elliotf/cranestyle-mini/renders/x-min-cover.stl

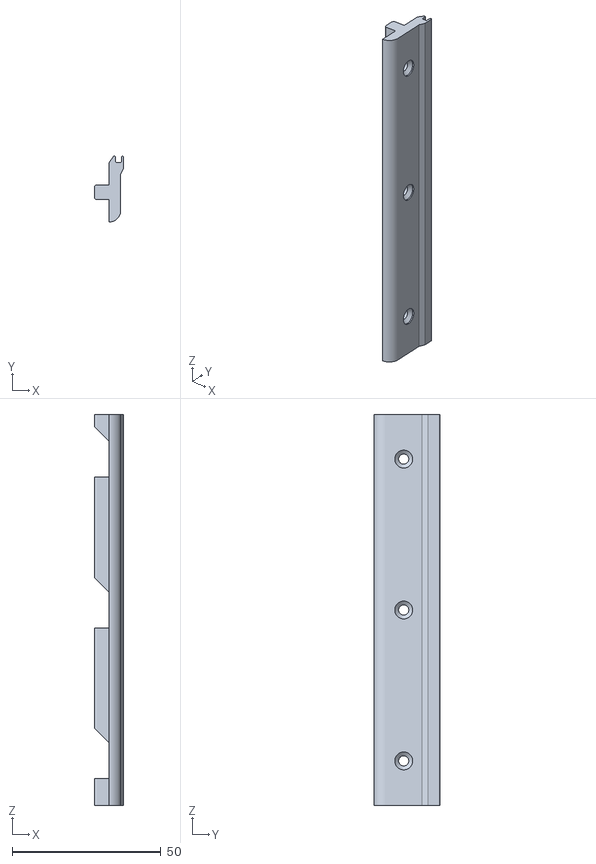
[picture p15: CAD file, 2019-06-30]
renders/x-min-cover.stl
9.90 x 22.2 x 131.5
