elliotf/cranestyle-mini/walter/Left Extruder Cable Clip.stl

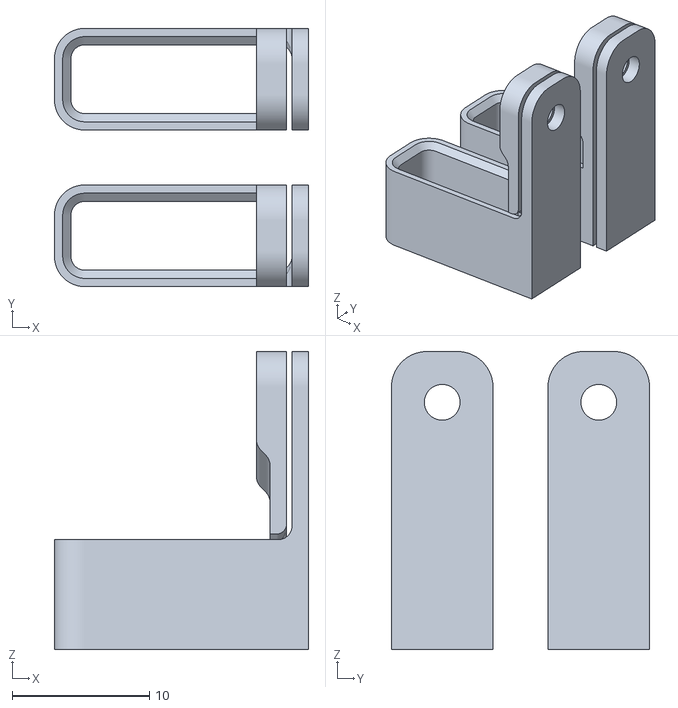
[picture p16: CAD file, 2019-05-31]
walter/Left Extruder Cable Clip.stl
18.5 x 18.8 x 21.7
