elliotf/cranestyle-mini/renders/y-endstop-mount.stl

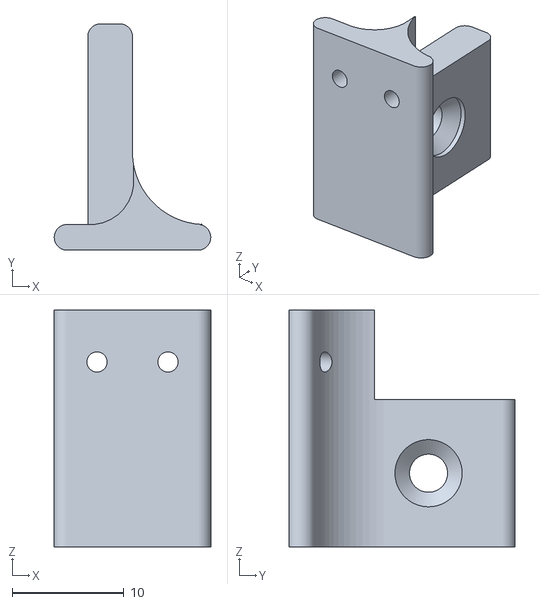
[picture p17: CAD file, 2019-06-30]
renders/y-endstop-mount.stl
14.0 x 20.2 x 21.2
