elliotf/cranestyle-mini/renders/x-max-cover.stl

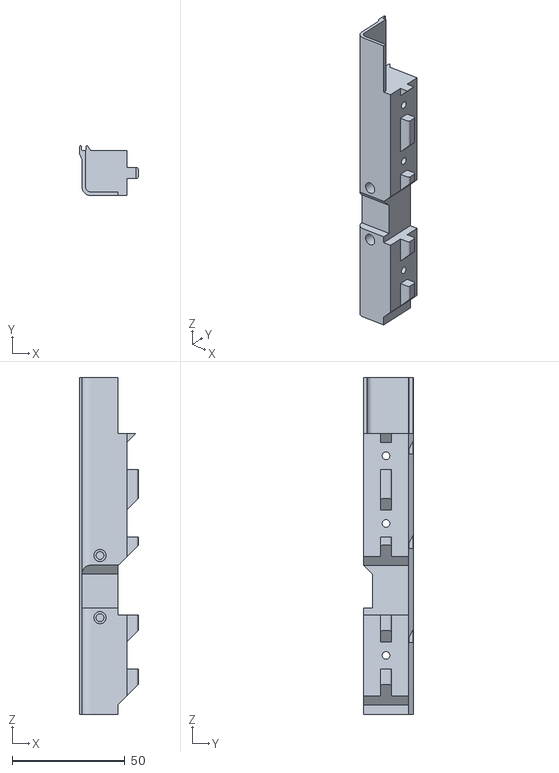
[picture p18: CAD file, 2019-06-30]
renders/x-max-cover.stl
26.0 x 22.2 x 149.5
