elliotf/cranestyle-mini/renders/z-motor-mount.stl

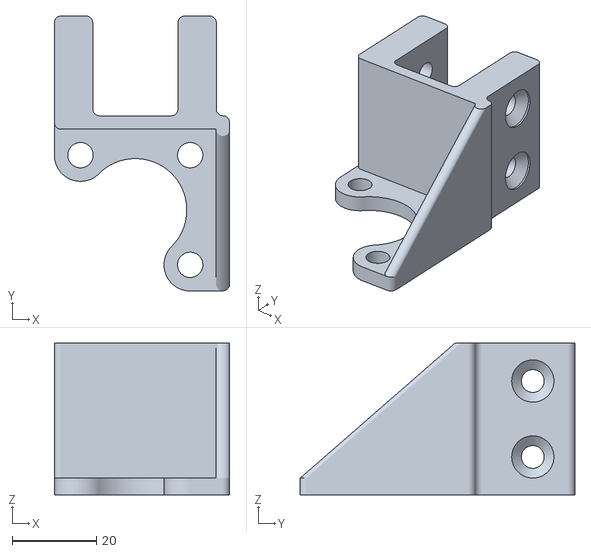
[picture p19: CAD file, 2019-06-30]
renders/z-motor-mount.stl
41.5 x 65.2 x 36.0
