elliotf/cranestyle-mini/renders/tnut-zip-tie-anchor.stl

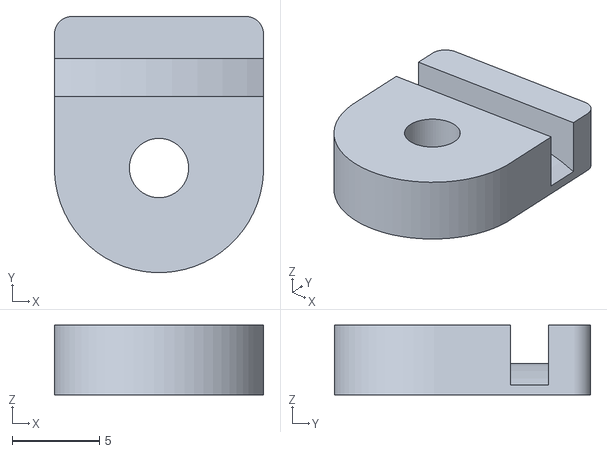
[picture p20: CAD file, 2019-06-30]
renders/tnut-zip-tie-anchor.stl
12.0 x 14.7 x 4.00
