elliotf/cranestyle-mini/renders/y-belt-carriage-mount.stl

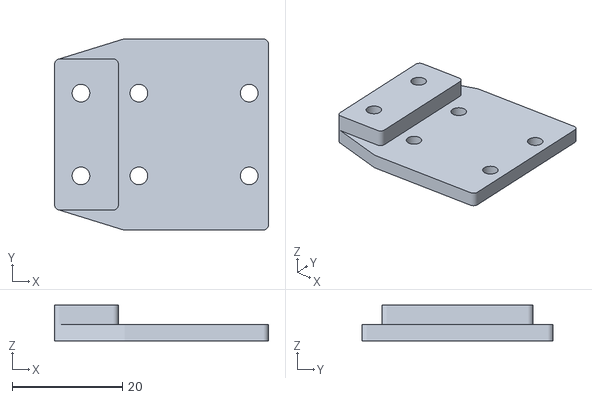
[picture p21: CAD file, 2019-06-30]
renders/y-belt-carriage-mount.stl
38.8 x 34.7 x 6.50
