elliotf/cranestyle-mini/renders/end-cap-rear.stl

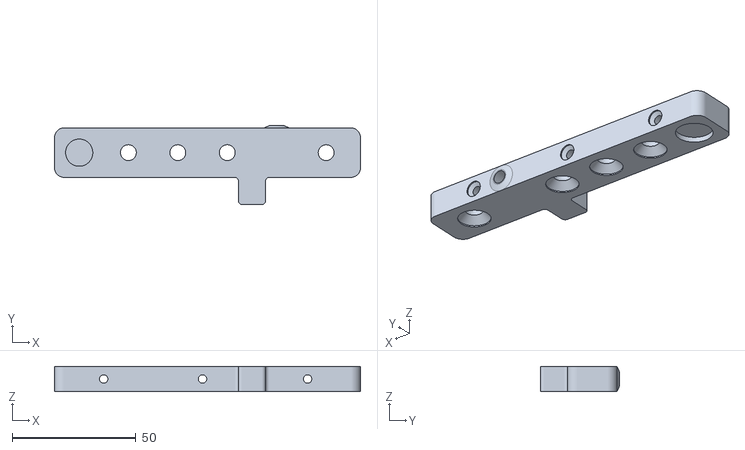
[picture p22: CAD file, 2019-06-30]
renders/end-cap-rear.stl
123.8 x 32.0 x 10.2
