elliotf/cranestyle-mini/renders/tnut-cable-clip.stl

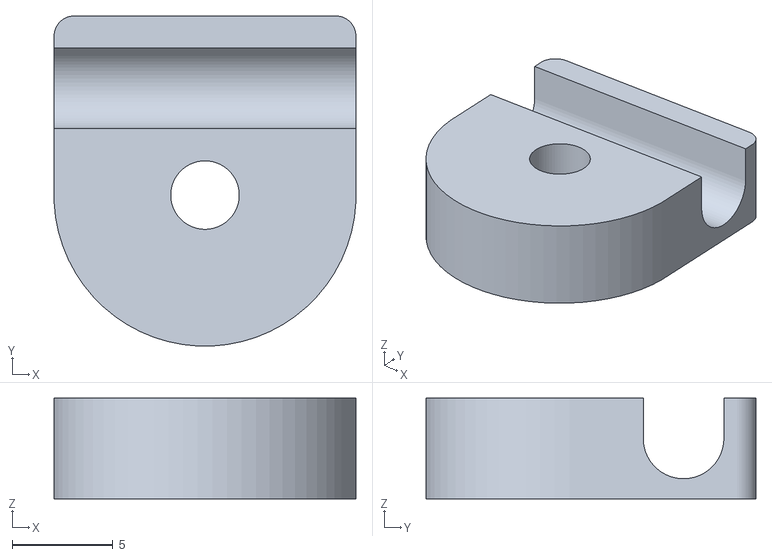
[picture p23: CAD file, 2019-06-30]
renders/tnut-cable-clip.stl
15.0 x 16.4 x 5.00
