elliotf/cranestyle-mini/renders/extruder-motor-plate.stl

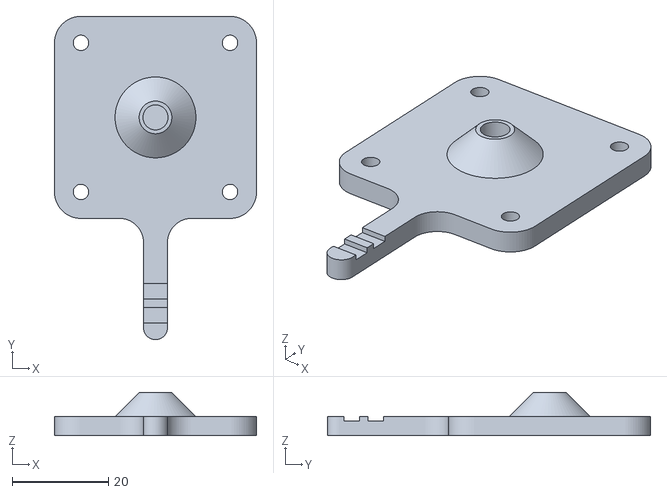
[picture p24: CAD file, 2019-06-30]
renders/extruder-motor-plate.stl
42.0 x 67.2 x 9.00
