elliotf/cranestyle-mini/renders/y-belt-clamp.stl

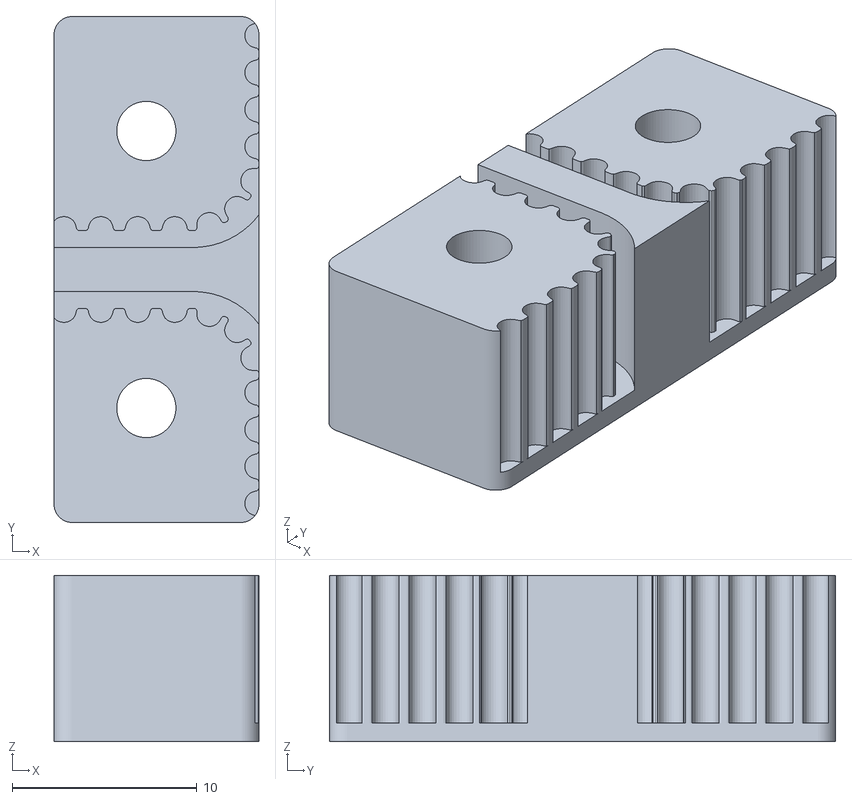
[picture p25: CAD file, 2019-06-30]
renders/y-belt-clamp.stl
11.1 x 27.4 x 9.00
