elliotf/cranestyle-mini/renders/x-idler.stl

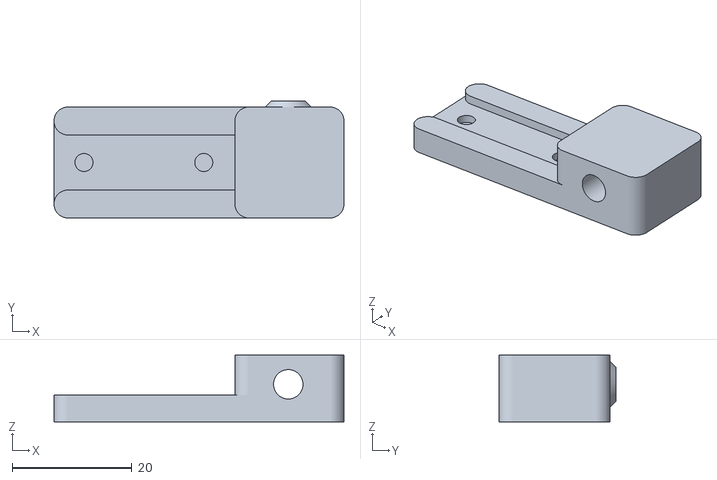
[picture p26: CAD file, 2019-06-30]
renders/x-idler.stl
48.4 x 19.5 x 11.1
