elliotf/cranestyle-mini/renders/tslot-filler.stl

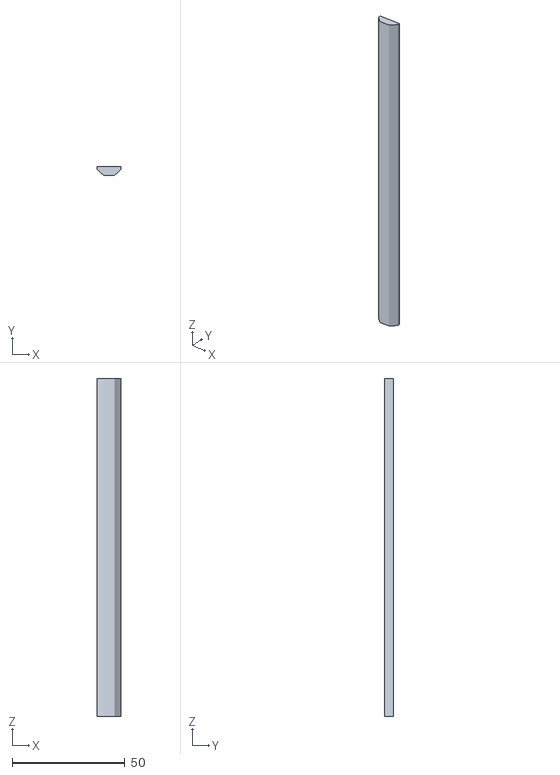
[picture p27: CAD file, 2019-06-15]
renders/tslot-filler.stl
10.6 x 3.80 x 150.0
