elliotf/cranestyle-mini/renders/hotend-fan-mount.stl

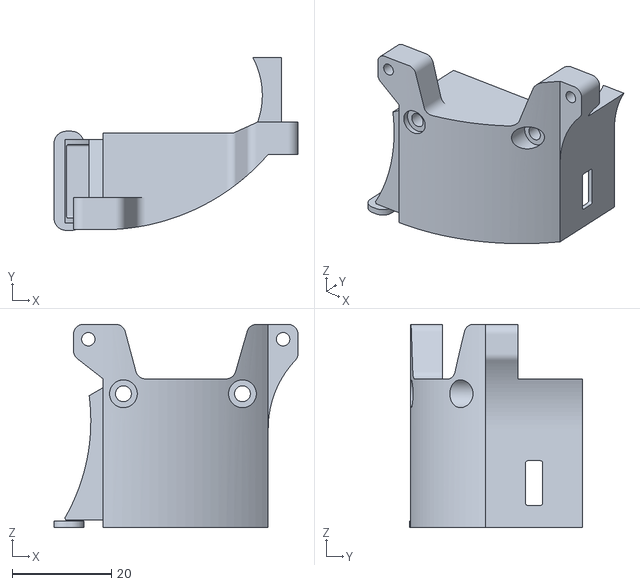
[picture p28: CAD file, 2019-06-15]
renders/hotend-fan-mount.stl
49.2 x 34.9 x 41.0
