elliotf/cranestyle-mini/renders/tnut-cable-anchor.stl

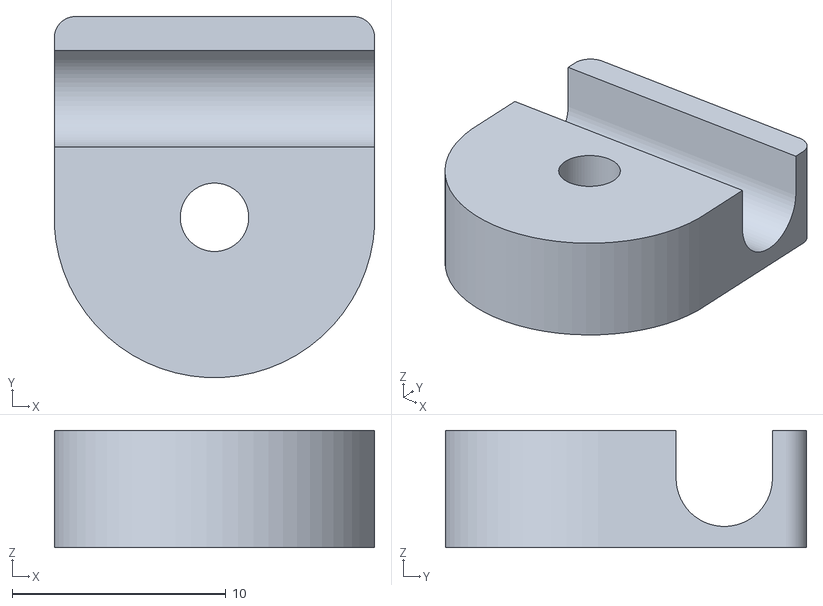
[picture p29: CAD file, 2019-06-06]
renders/tnut-cable-anchor.stl
15.0 x 16.9 x 5.50
