elliotf/cranestyle-mini/renders/m2-tnut.stl

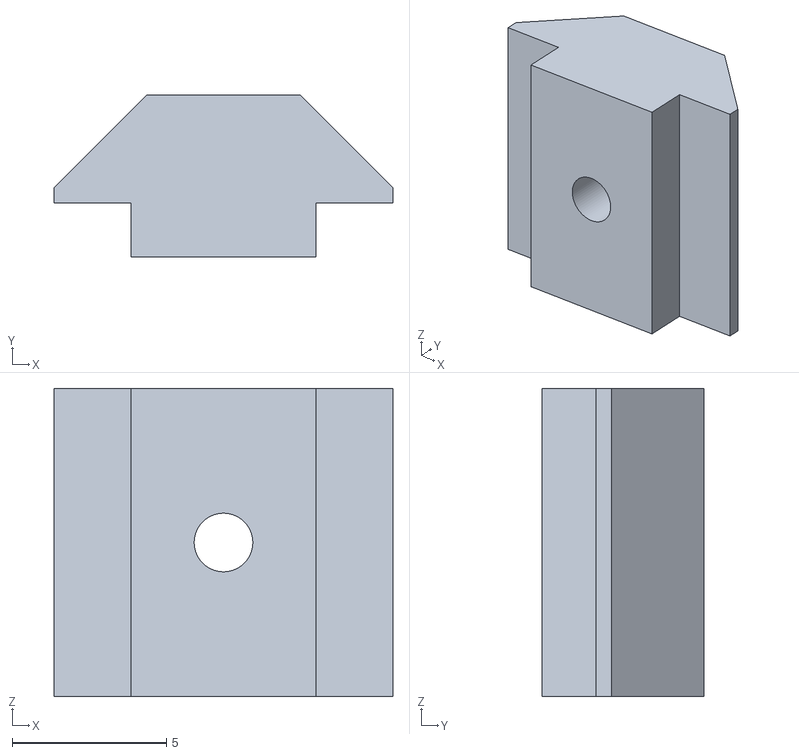
[picture p30: CAD file, 2019-06-04]
renders/m2-tnut.stl
11.0 x 5.25 x 10.0
