elliotf/cranestyle-mini/for_render/extruder-motor-plate.scad

use <../extruder-mount.scad>;

extruder_motor_plate_to_print();
