elliotf/cranestyle-mini/for_render/x-motor-threaded-insert-nut-holder.scad

color("lightblue") import("../walter/20mm Nut Holder.stl");
