elliotf/cranestyle-mini/for_render/y-motor-mount.scad

use <../y-motor-mount.scad>;

to_print();
