elliotf/cranestyle-mini/for_render/z-motor-mount.scad

use <../z-motor-mount.scad>;

to_print();
