elliotf/cranestyle-mini/for_render/bottom_cover.scad

include <../config.scad>;
include <../lib/util.scad>;
use <../end-caps.scad>;

bottom_cover();
