elliotf/cranestyle-mini/for_render/duet-mount.scad

use <../duet-wifi-mount.scad>;

to_print();
