elliotf/cranestyle-mini/for_render/end-cap-rear.scad

include <../config.scad>;
include <../lib/util.scad>;
use <../end-caps.scad>;

rotate([-90,0,0]) {
  end_cap_rear();
}
