elliotf/cranestyle-mini/for_render/extruder-bracket.scad

use <../extruder-mount.scad>;

extruder_bracket_to_print();
