elliotf/cranestyle-mini/for_render/extruder-swivel.scad

use <../extruder-mount.scad>;

extruder_swivel_to_print();
