elliotf/cranestyle-mini/for_render/handle.scad

use <../handle.scad>;

handle();
