elliotf/cranestyle-mini/for_render/hotend-fan-mount.scad

use <../hotend-fan-mount.scad>;

hotend_fan_mount_to_print();
