elliotf/cranestyle-mini/for_render/m2-tnut.scad

use <../tnuts.scad>;

m2_tnut();
