elliotf/cranestyle-mini/for_render/part-cooling-duct.scad

translate([0,0,28.1]) {
  rotate([0,52,0]) {
    color("lightblue") import("../walter/Cooling Duct.stl");
  }
}
