elliotf/cranestyle-mini/for_render/tnut-cable-clip.scad

use <../tslot-stuff.scad>;

tnut_cable_anchor(4);
