elliotf/cranestyle-mini/for_render/tnut-m2-nut.scad

use <../tnuts.scad>;

tnut_m2();
