elliotf/cranestyle-mini/for_render/tnut-zip-tie-anchor.scad

use <../tslot-stuff.scad>;

tnut_zip_tie_anchor();
