elliotf/cranestyle-mini/for_render/tslot-filler.scad

use <../tslot-stuff.scad>;

tslot_filler(150);
