elliotf/cranestyle-mini/for_render/x-carriage-belt-tensioner.scad

use <../x-carriage.scad>;

carriage_belt_tensioner_to_print();
