elliotf/cranestyle-mini/for_render/x-carriage.scad

use <../x-carriage.scad>;

carriage_to_print();
