elliotf/cranestyle-mini/for_render/x-idler.scad

use <../x-idler.scad>;

to_print();
