elliotf/cranestyle-mini/for_render/x-max-cover.scad

include <../config.scad>;
include <../lib/util.scad>;
use <../end-caps.scad>;

rotate([90,0,0]) {
  x_min_cover();
}
