elliotf/cranestyle-mini/for_render/y-belt-carriage-mount.scad

use <../y-carriage.scad>;

rotate([180,0,0]) {
  mgn_clamp_mount();
}
