elliotf/cranestyle-mini/for_render/y-belt-clamp.scad

use <../y-carriage.scad>;

belt_clamp();
