elliotf/cranestyle-mini/for_render/y-carriage-printed.scad

use <../y-carriage.scad>;

rotate([0,180,0]) {
  printed_y_carriage();
}
