elliotf/cranestyle-mini/for_render/y-endstop-mount.scad

use <../y-endstop-mount.scad>;

to_print();
