elliotf/cranestyle-mini/for_render/z-nut-mount.scad

use <../z-nut-mount.scad>;

to_print();
